koko69420/HomeBus/Hardware/Expanders/Expanders-F_Cu.pdf

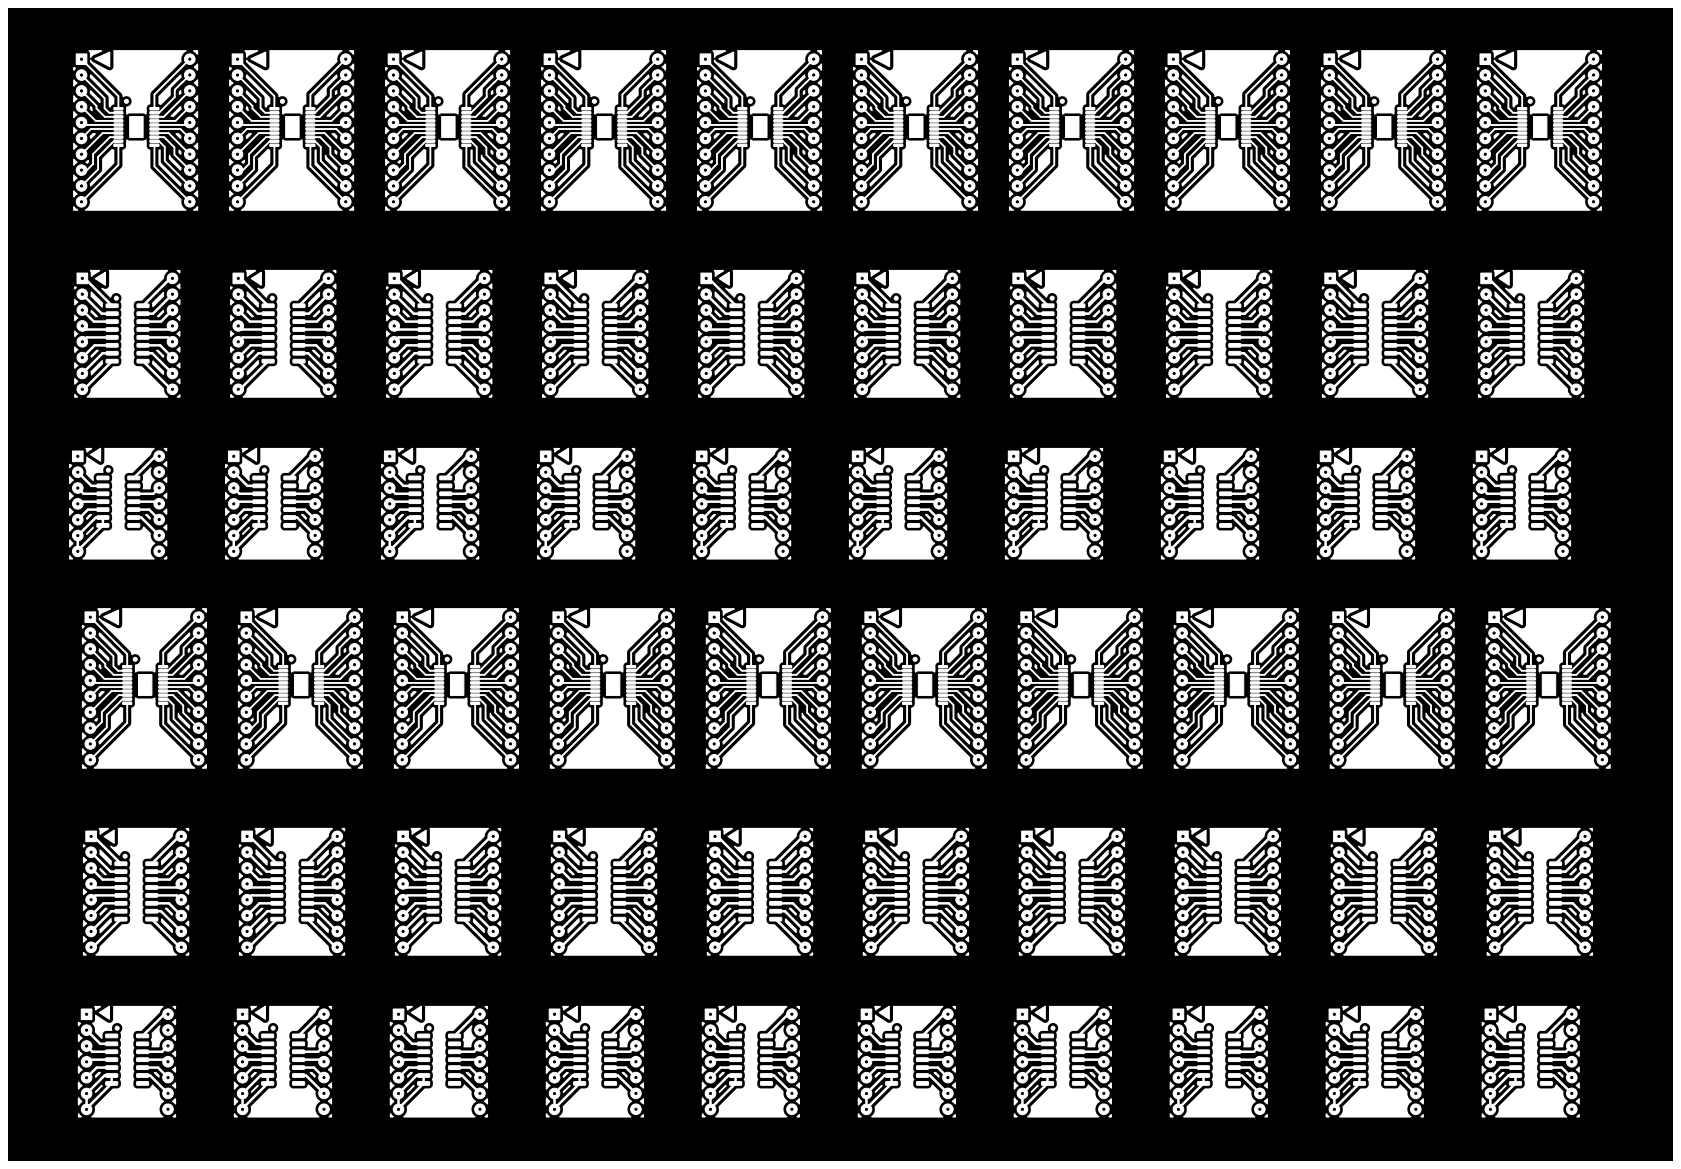
[picture p19: page 1]
