koko69420/HomeBus/Hardware/Expanders/Expanders-F_Paste.pdf

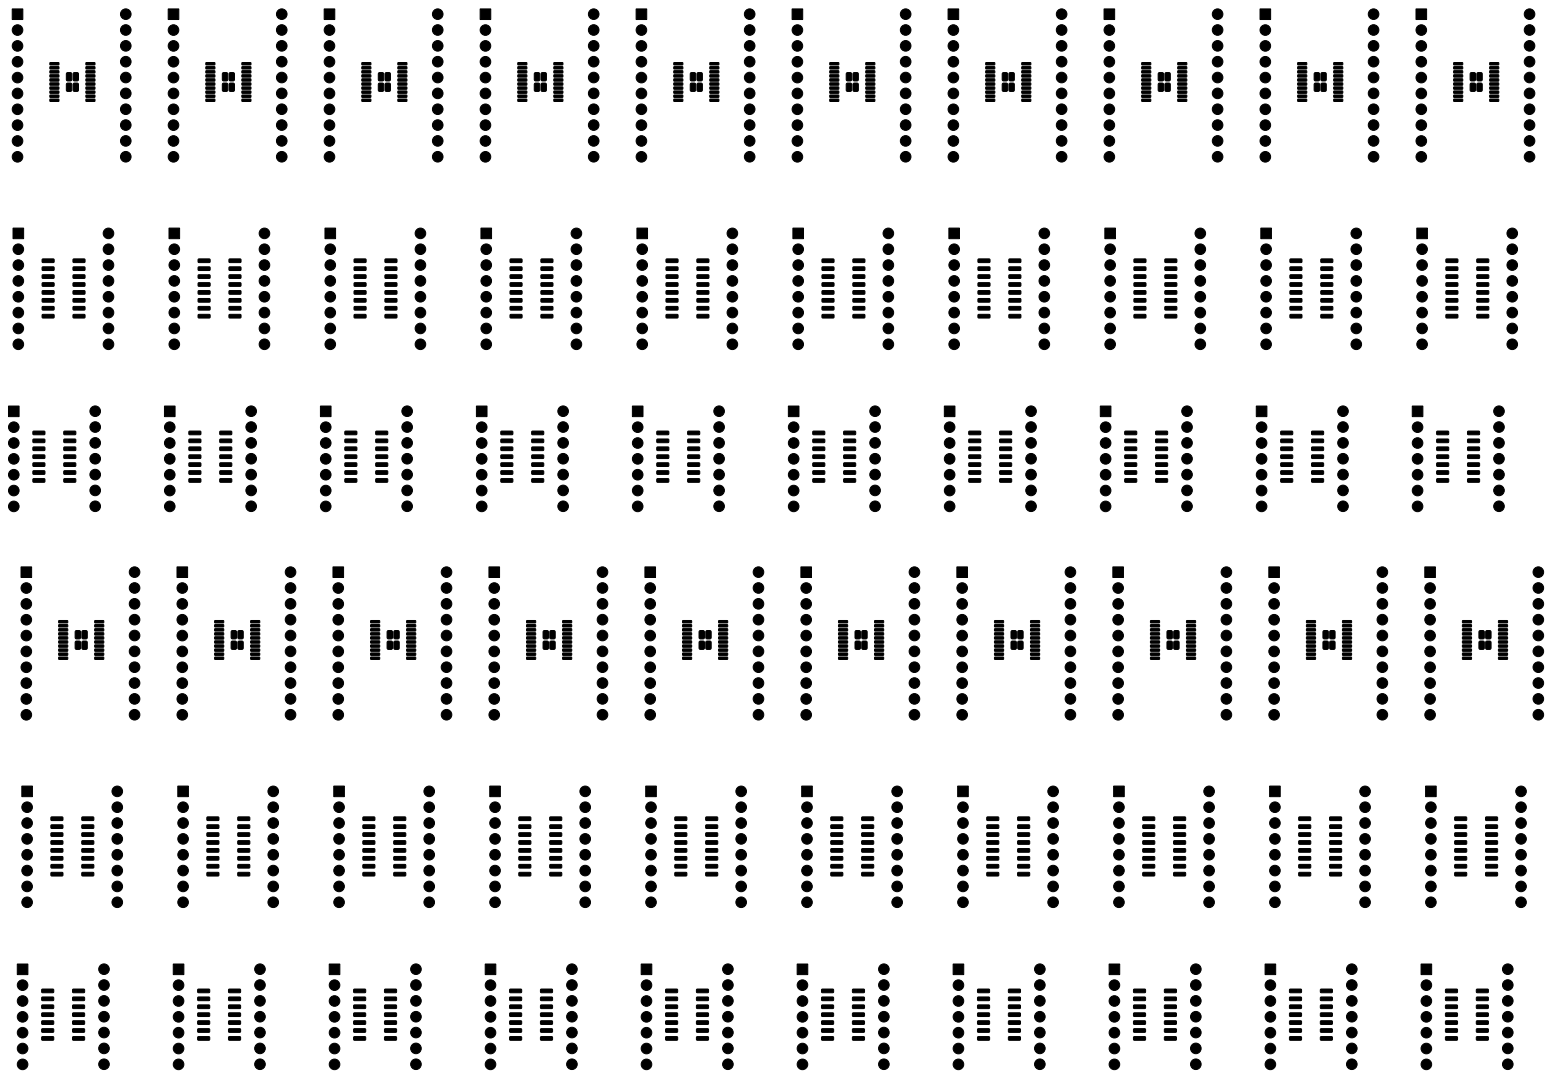
[picture p20: page 1]
