koko69420/HomeBus/Hardware/Gateway_node/Gateway_node_dev-board/Gateway_node_dev-board-B_Cu.pdf

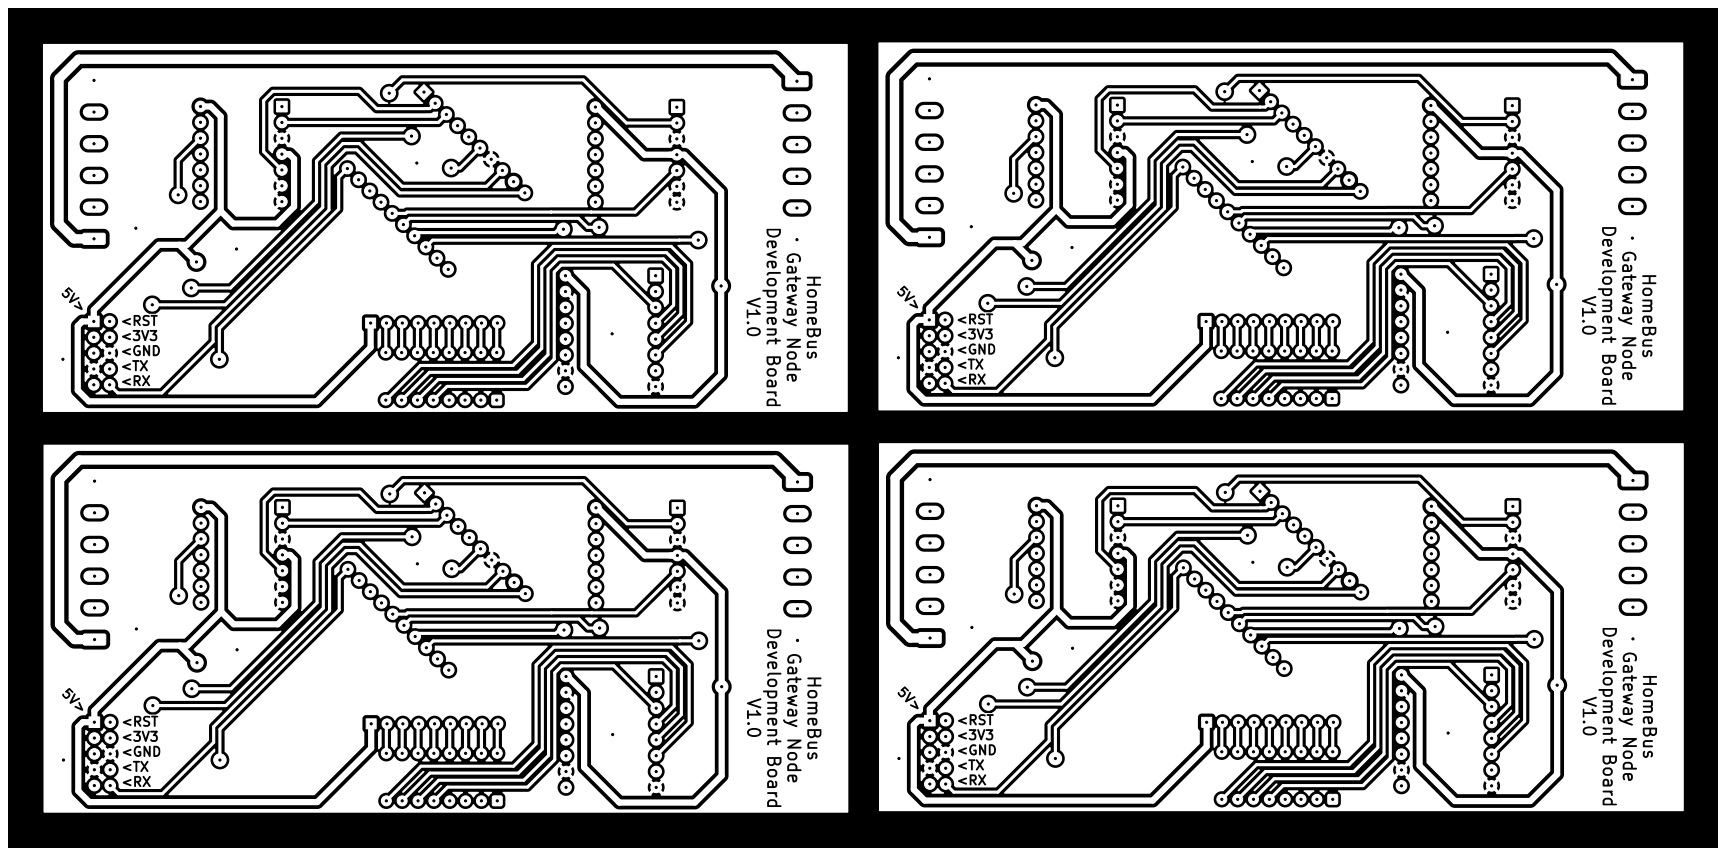
[picture p21: page 1]
