koko69420/HomeBus/Hardware/Gateway_node/Gateway_node_dev-board/Gateway_node_dev-board-Edge_Cuts.pdf

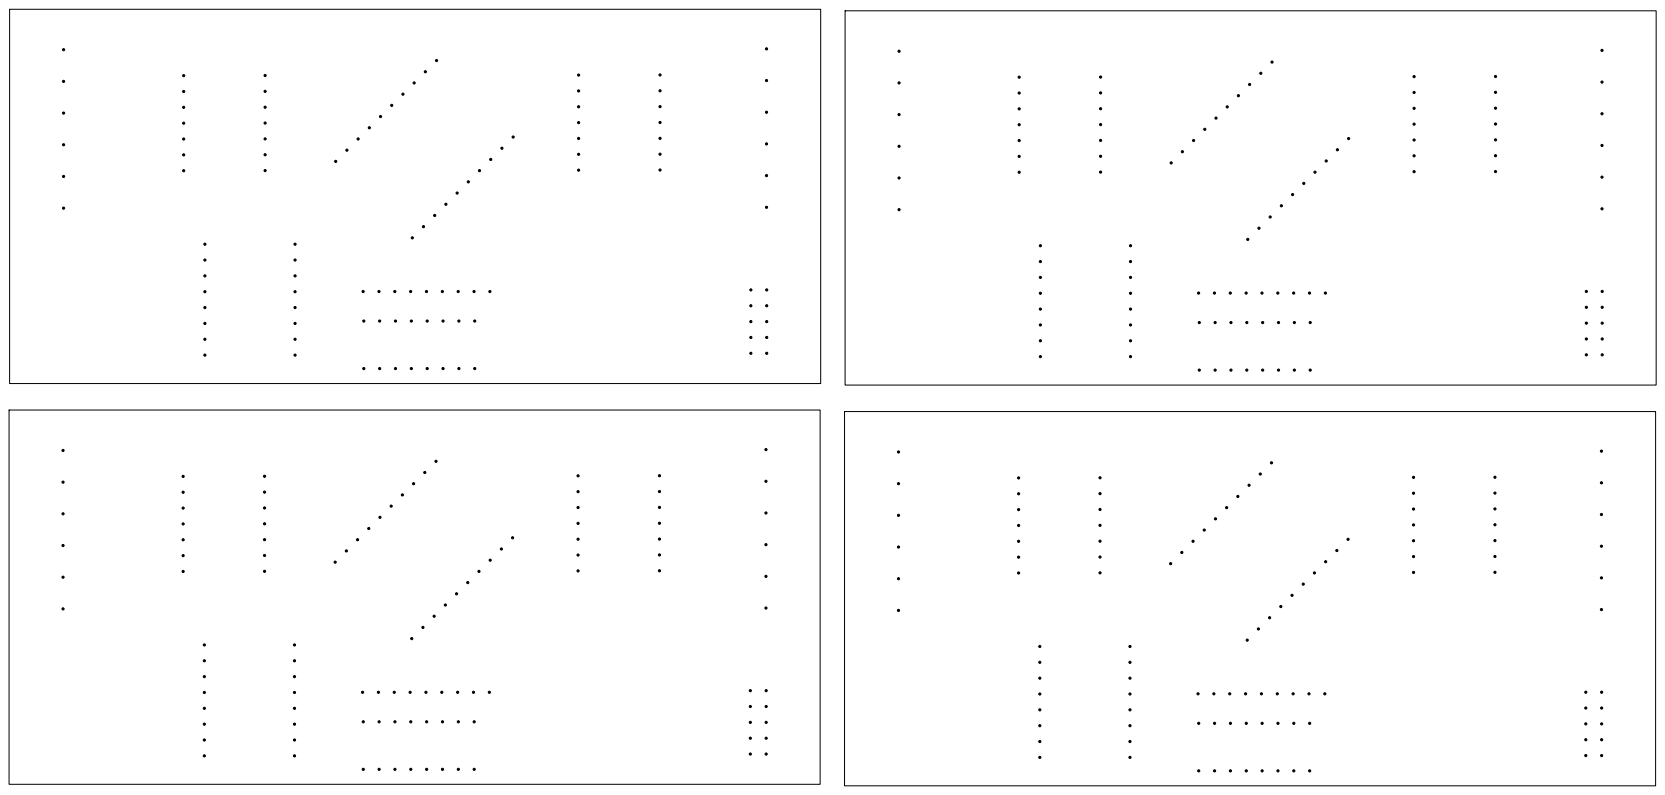
[picture p22: page 1]
