koko69420/HomeBus/Hardware/Gateway_node/Gateway_node_dev-board/Gateway_node_dev-board-F_Cu.pdf

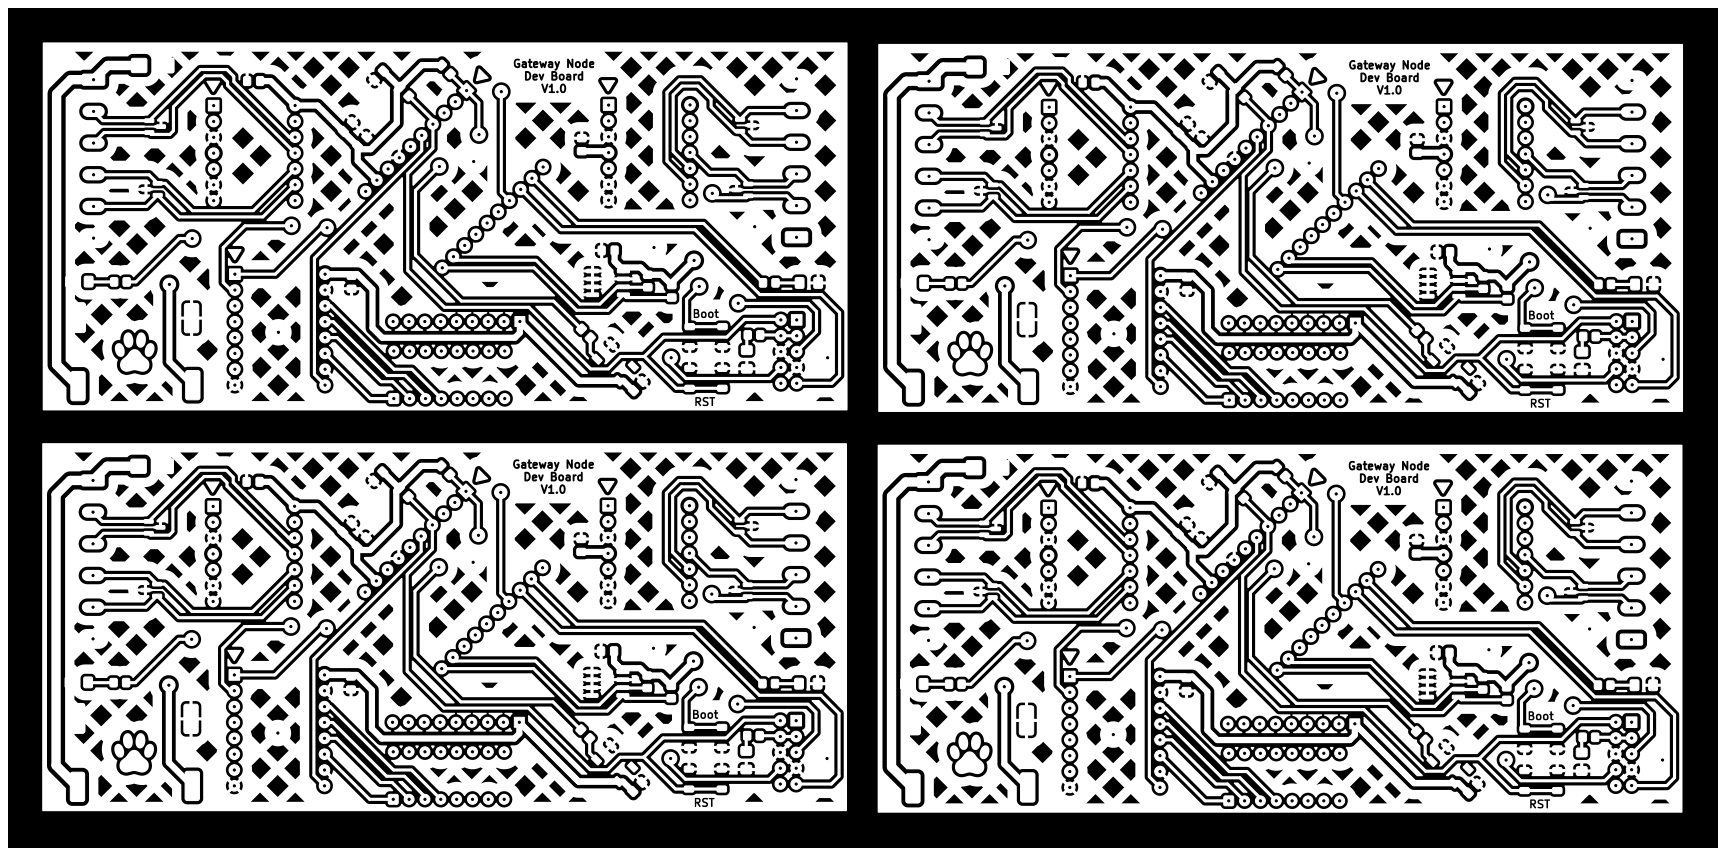
[picture p23: page 1]
