koko69420/HomeBus/Hardware/base_node/base_node_clad-B_Cu.pdf

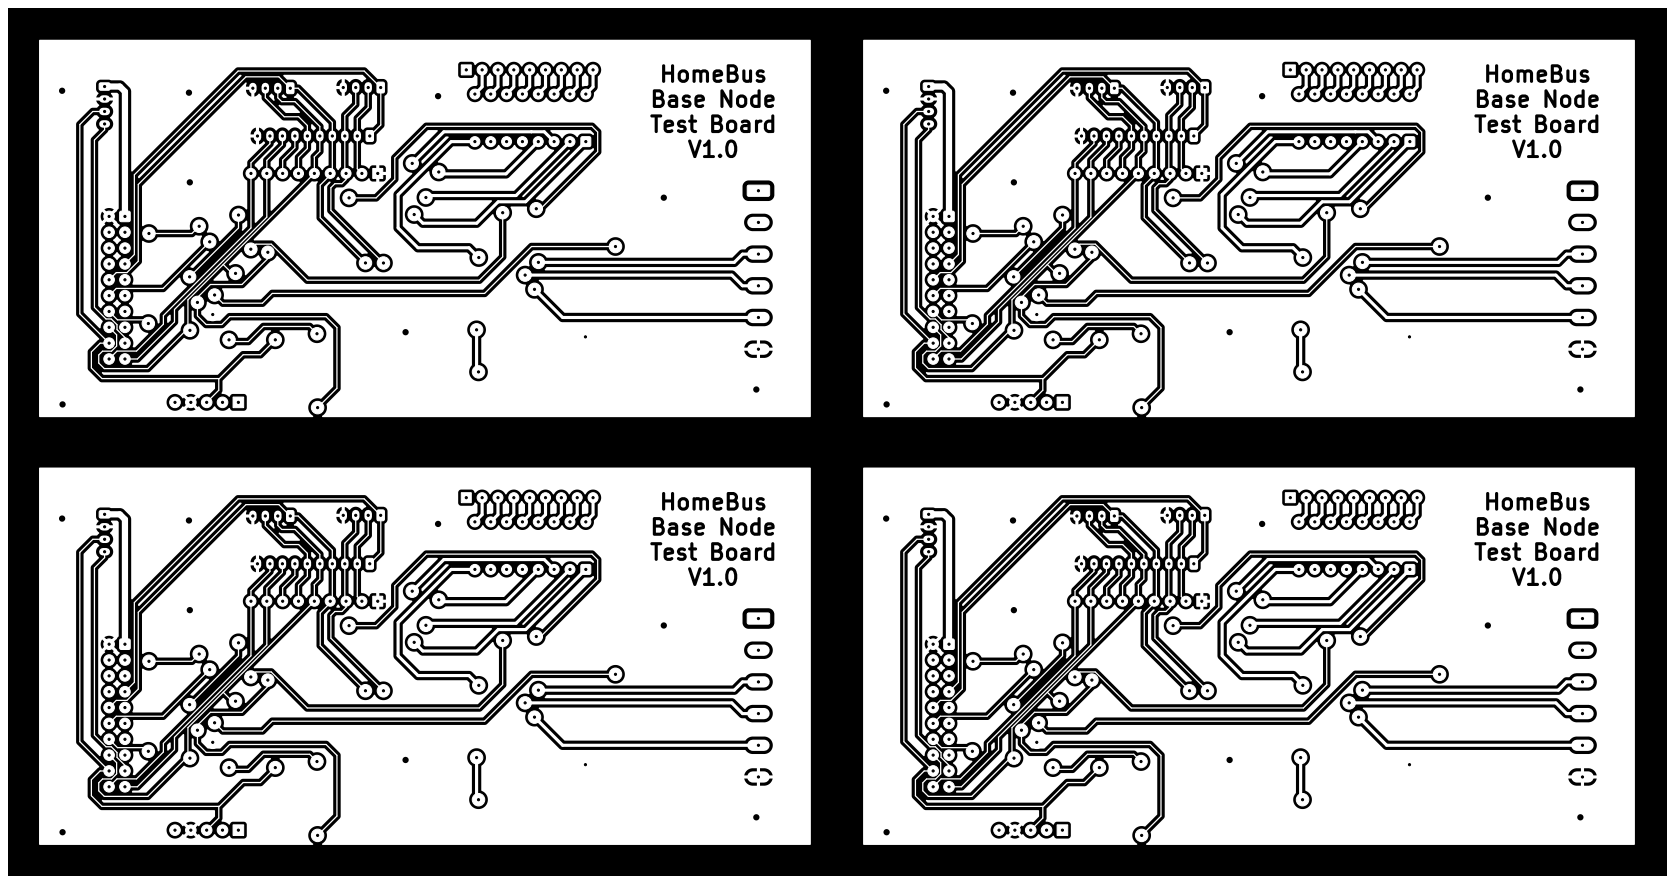
[picture p24: page 1]
