koko69420/HomeBus/Hardware/base_node/base_node_clad-F_Cu.pdf

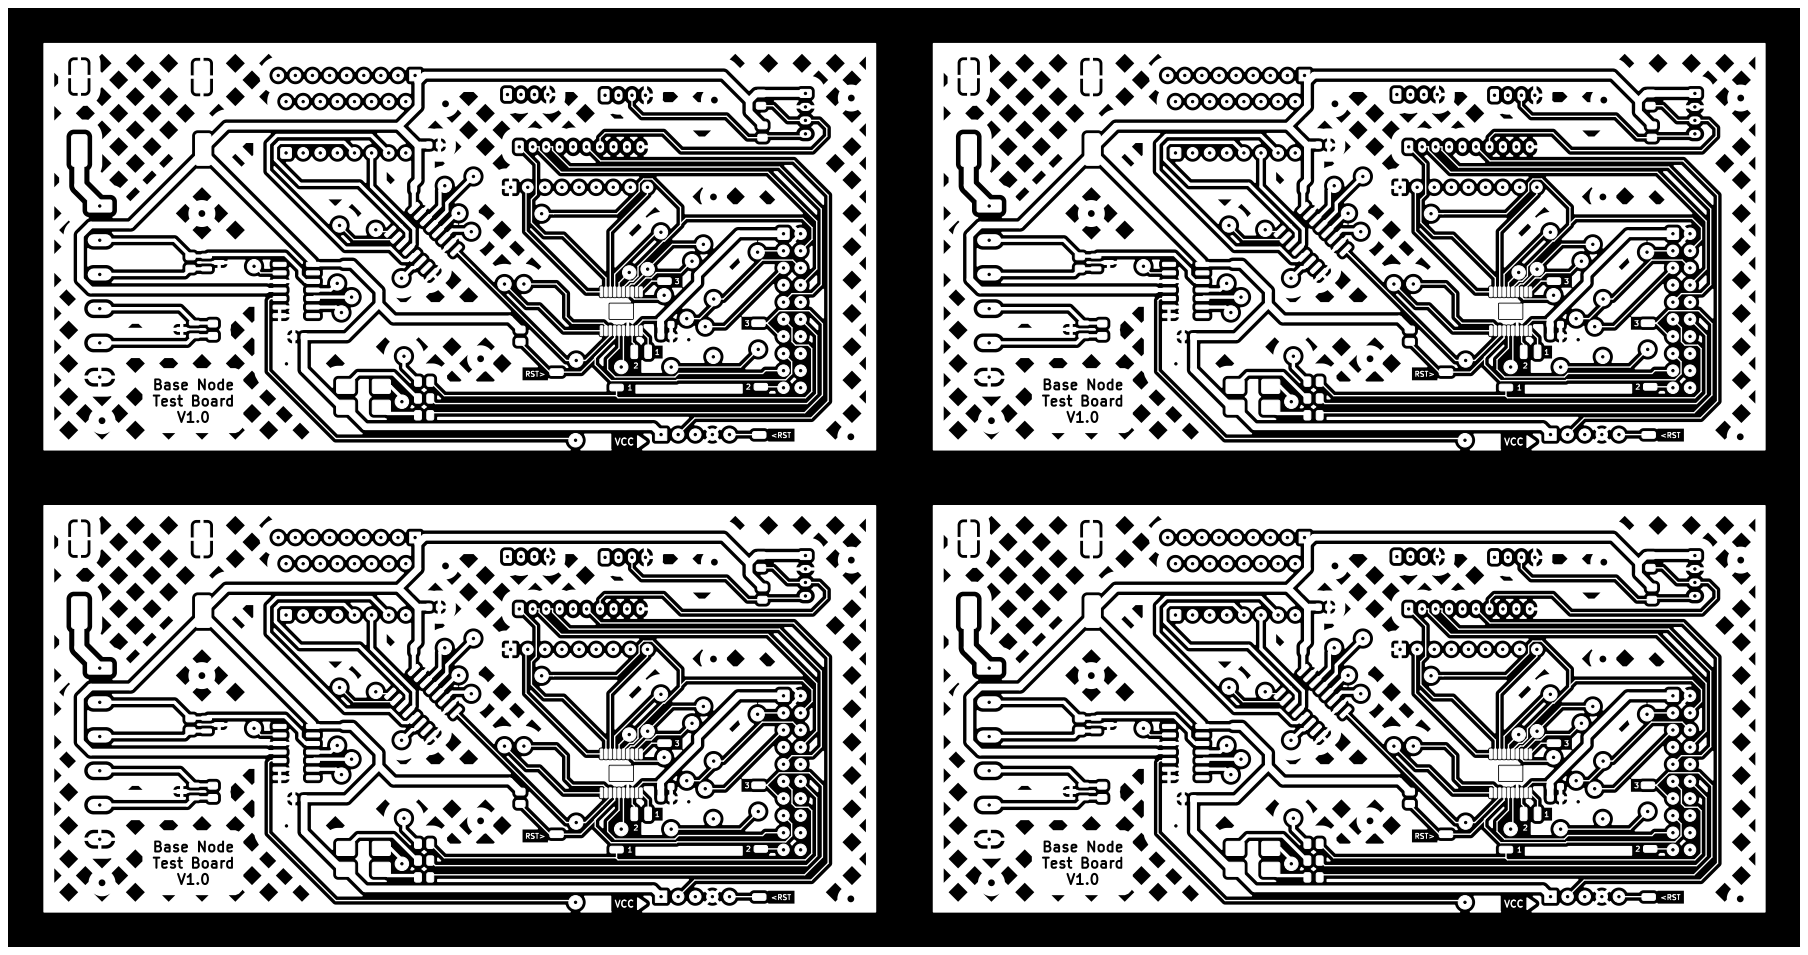
[picture p25: page 1]
